ymkn/JIS60-Split-Wing/img/guide-bottomplate_R-front.png

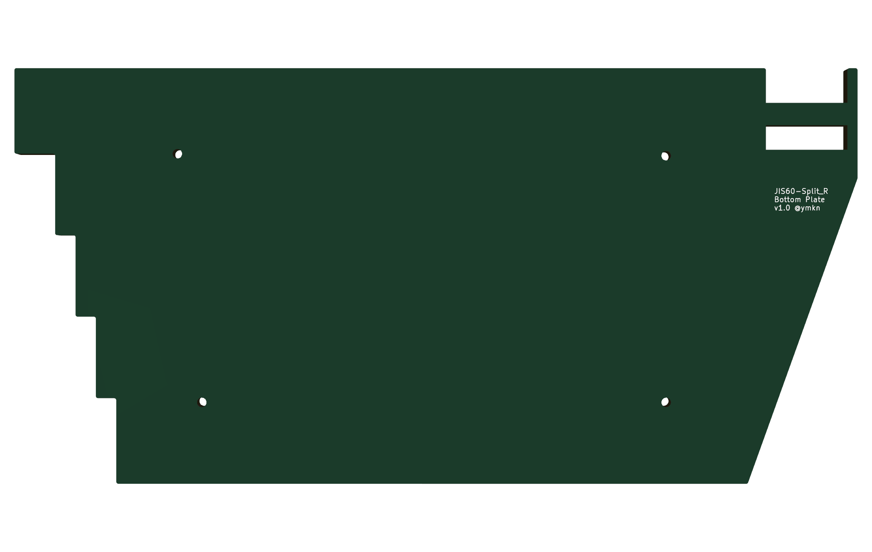
img/guide-bottomplate_R-front.png
