ymkn/JIS60-Split-Wing/img/guide-topplate_L-front.png

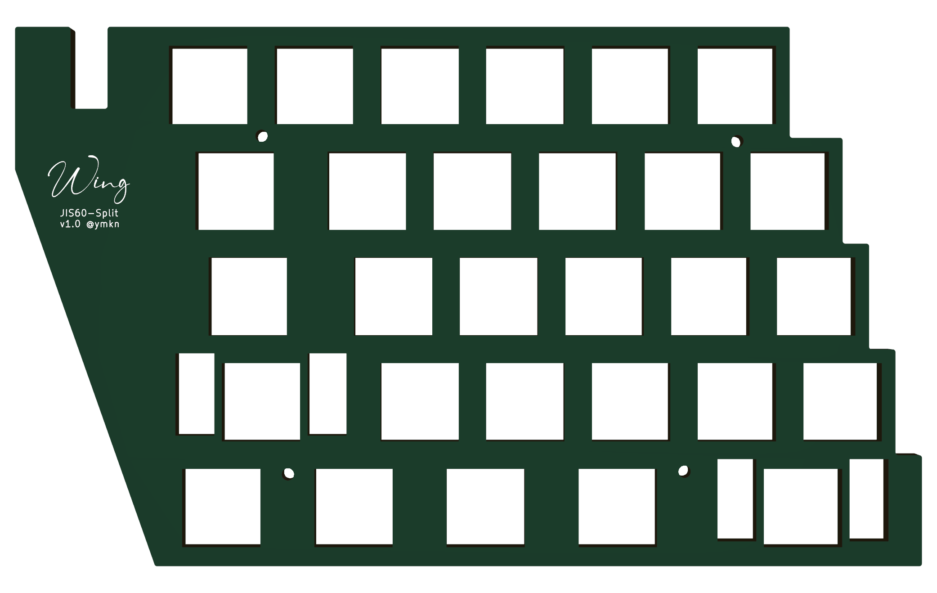
img/guide-topplate_L-front.png
